peter-dye/pd40-keyboard/Images/weaving_cathodes.jpeg

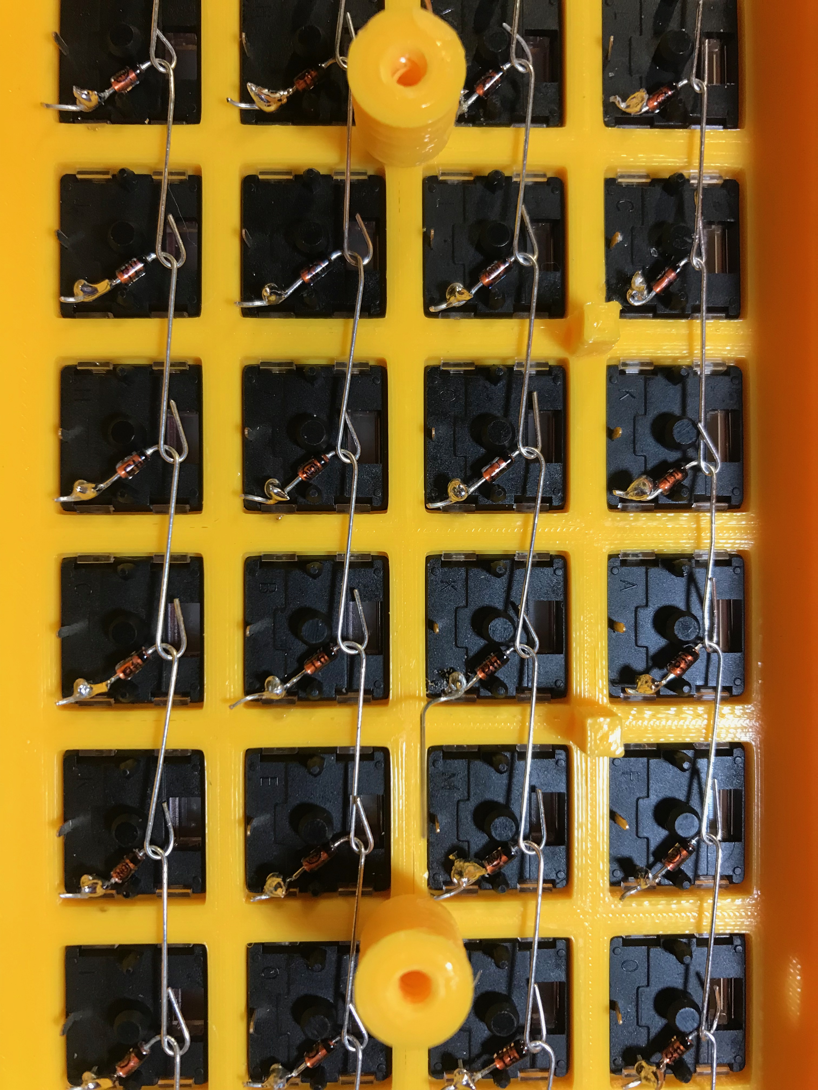
Images/weaving_cathodes.jpeg
